ManosDim/.Tangible-sequencer-with-vibrotactile-feedback/cad design/3.jpg

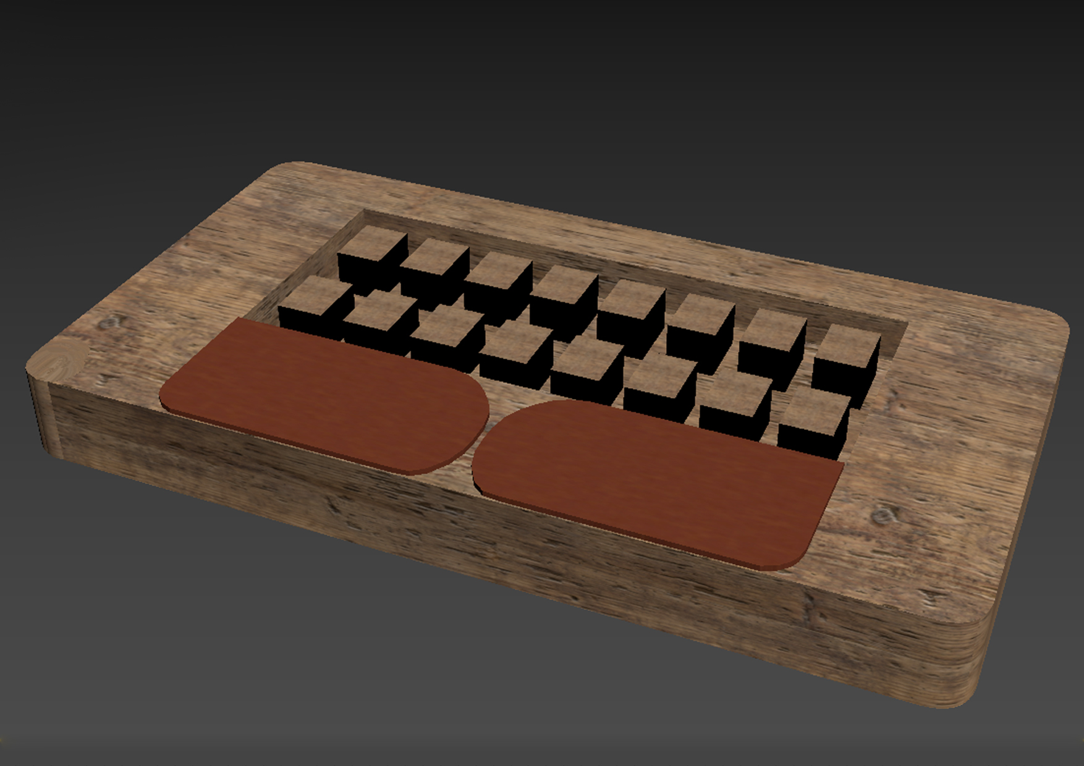
cad design/3.jpg
